ThingySticks/DisplayStick/Photon/V1/Images/PcbBottom.png

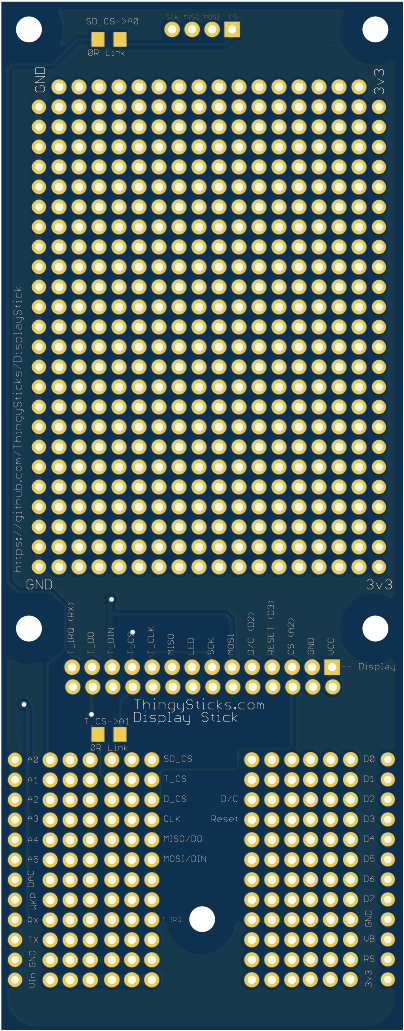
Photon/V1/Images/PcbBottom.png
