ThingySticks/DisplayStick/Photon/V1/Images/v1.0/PCB-Bottom.png

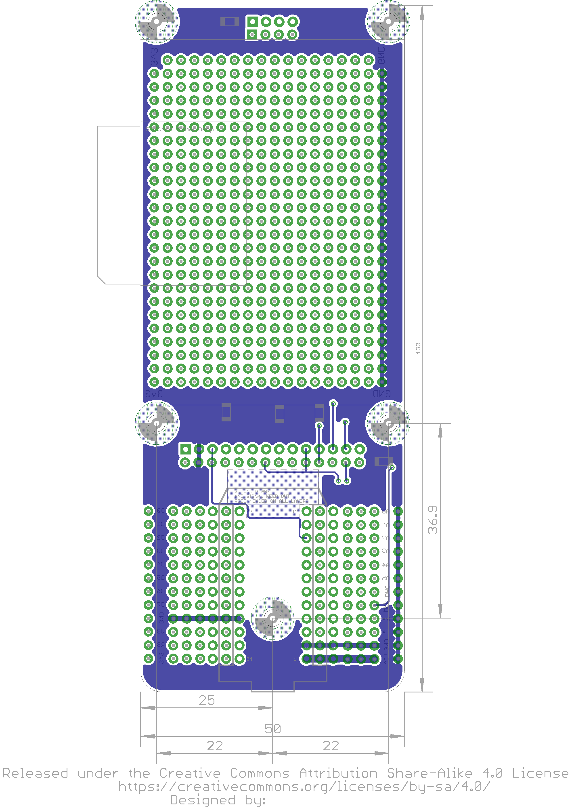
Photon/V1/Images/v1.0/PCB-Bottom.png
