ThingySticks/DisplayStick/Photon/V1/Images/v1.0/PCB-Top.png

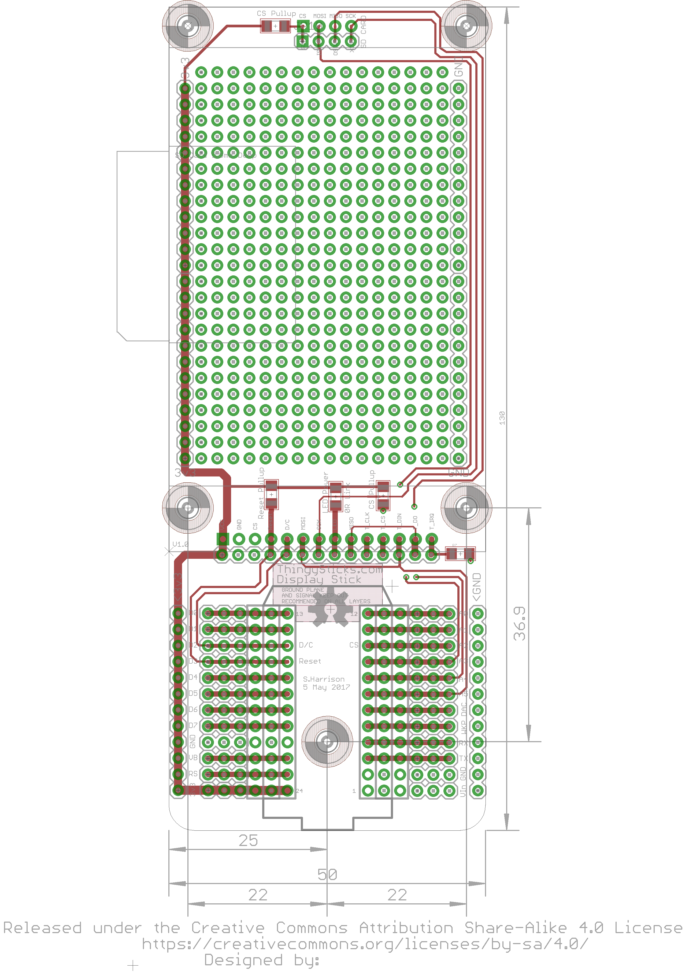
Photon/V1/Images/v1.0/PCB-Top.png
